cgowen/arcade/Build Photos/IMG_20240721_162805227.jpg

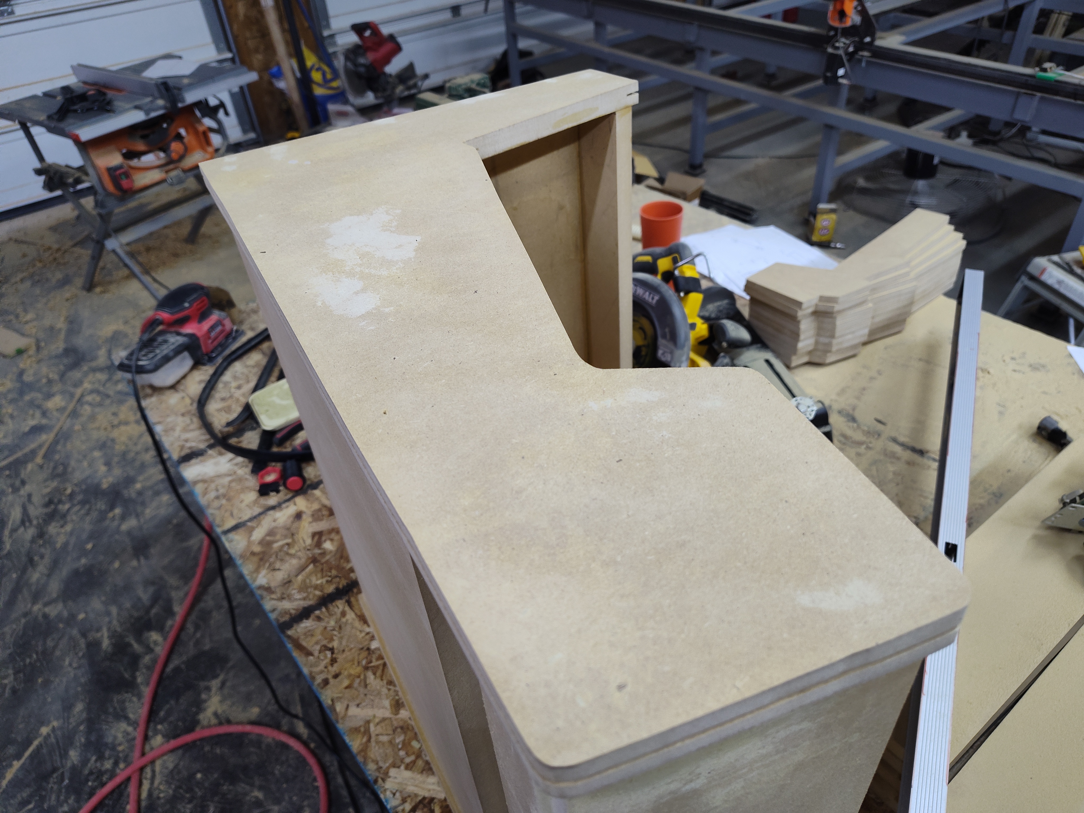
Build Photos/IMG_20240721_162805227.jpg
