cgowen/arcade/Build Photos/IMG_20240721_171913523_HDR.jpg

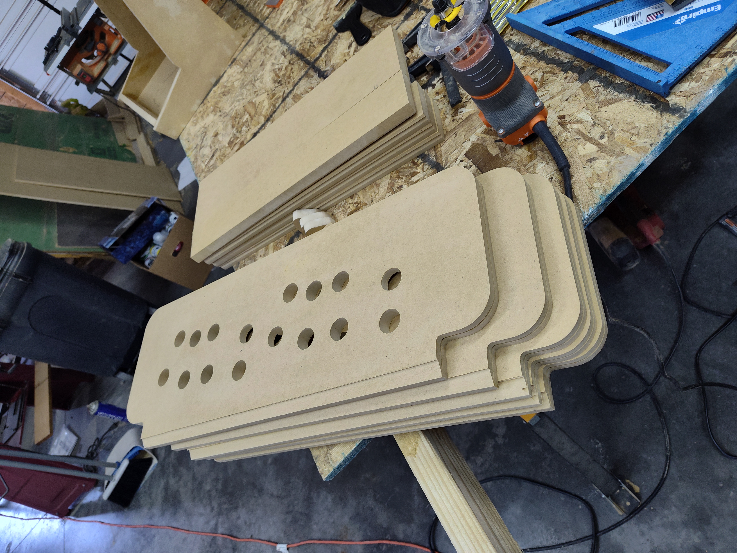
Build Photos/IMG_20240721_171913523_HDR.jpg
