cgowen/arcade/Build Photos/IMG_20240724_222536059_HDR.jpg

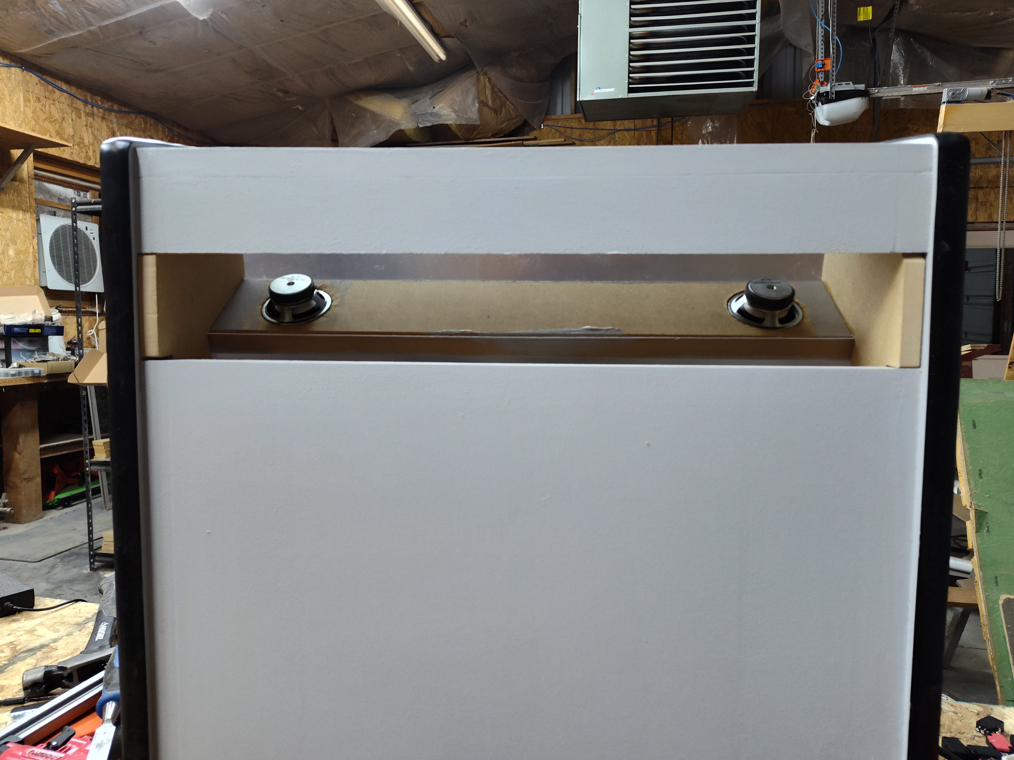
Build Photos/IMG_20240724_222536059_HDR.jpg
